cmz97/ai-eink/asciiTable_1.5x.png

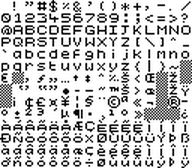
asciiTable_1.5x.png
