cmz97/ai-eink/asciiTable_2x.png

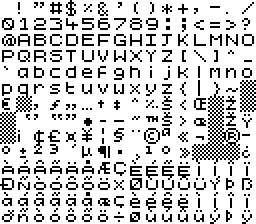
asciiTable_2x.png
