cmz97/ai-eink/asciiTable_3x.png

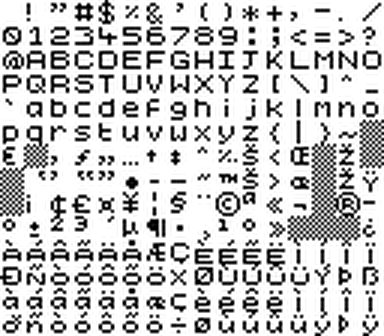
asciiTable_3x.png
