cmz97/ai-eink/Asset/Fav/3.png

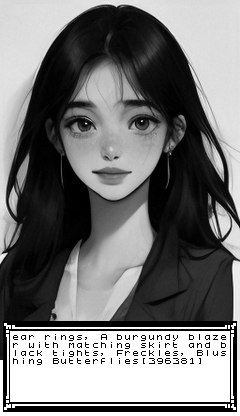
Asset/Fav/3.png
