cmz97/ai-eink/Asset/Fav/4.png

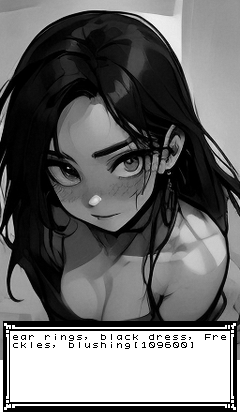
Asset/Fav/4.png
