cmz97/ai-eink/Asset/Fav/6.png

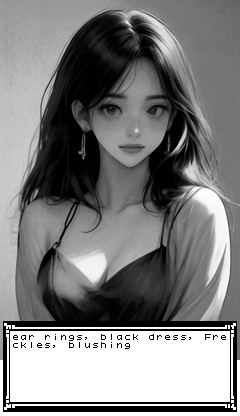
Asset/Fav/6.png
