cmz97/ai-eink/Asset/Fav/7.png

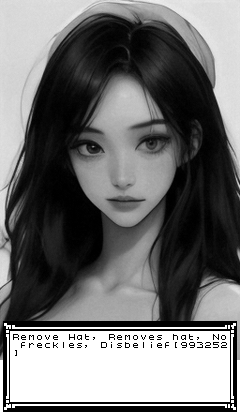
Asset/Fav/7.png
