cmz97/ai-eink/Asset/Fav/8.png

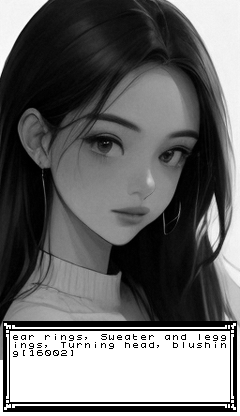
Asset/Fav/8.png
