cmz97/ai-eink/Asset/Fav/10.png

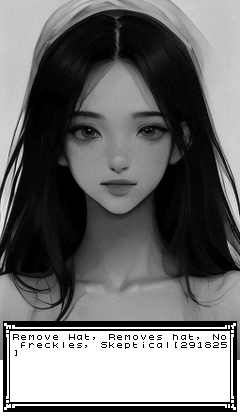
Asset/Fav/10.png
