cmz97/ai-eink/Asset/Fav/11.png

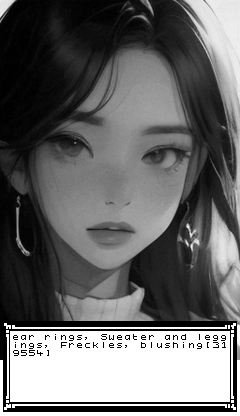
Asset/Fav/11.png
