cmz97/ai-eink/Asset/Fav/fr_00.png

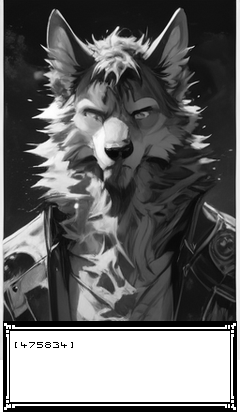
Asset/Fav/fr_00.png
