cmz97/ai-eink/Asset/Fav/men_00.png

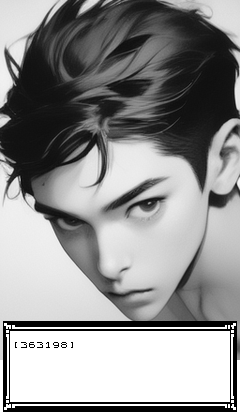
Asset/Fav/men_00.png
