cmz97/ai-eink/Asset/Fav/men_01.png

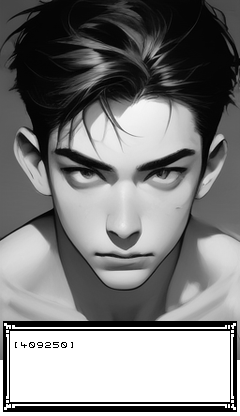
Asset/Fav/men_01.png
