cmz97/ai-eink/PCB/AI_EINK.png

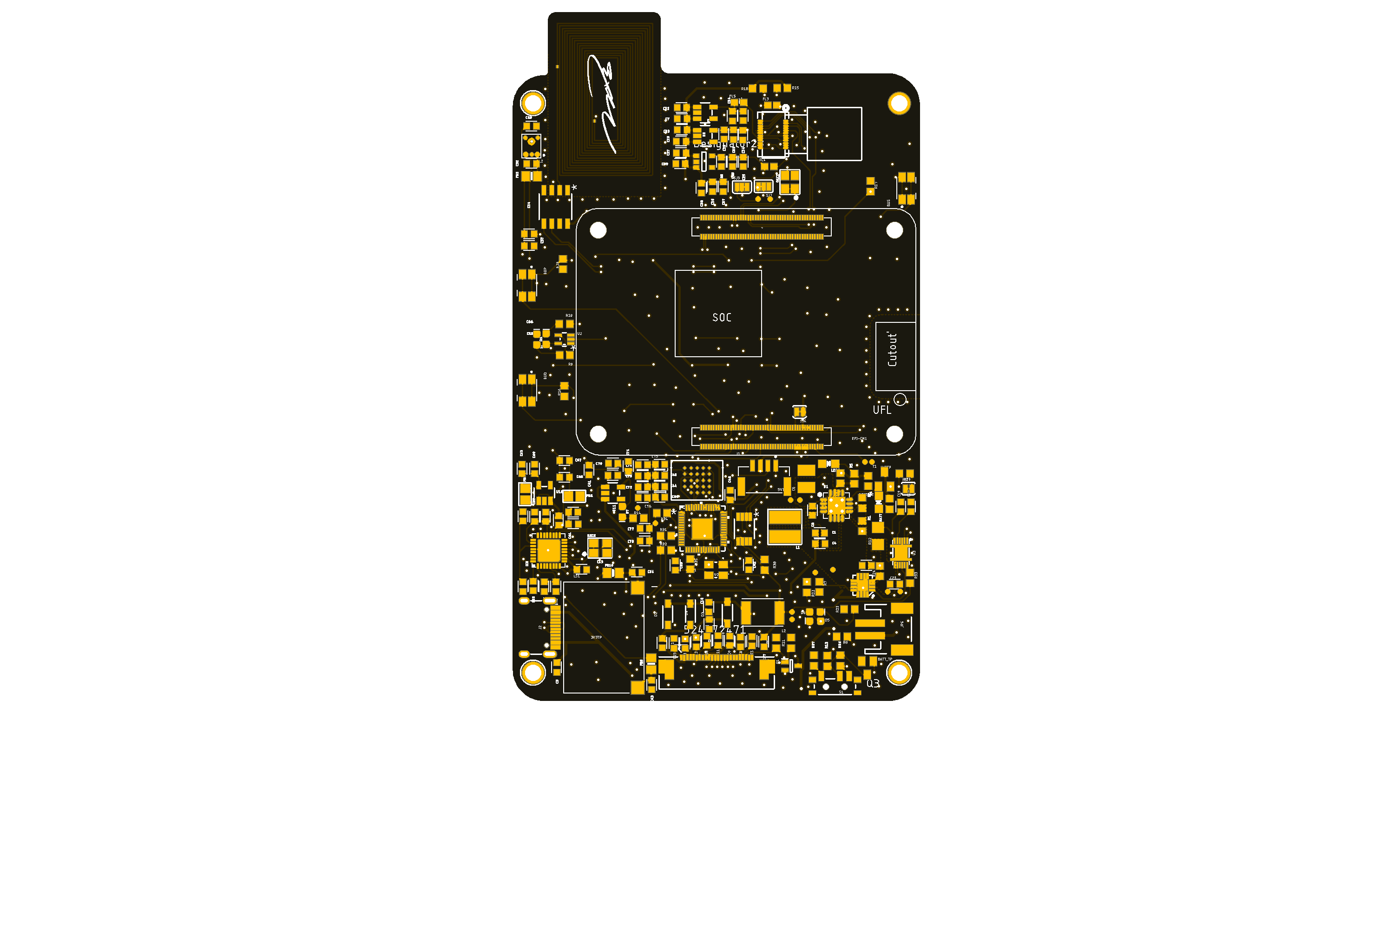
PCB/AI_EINK.png
