cmz97/ai-eink/Playground/1.png

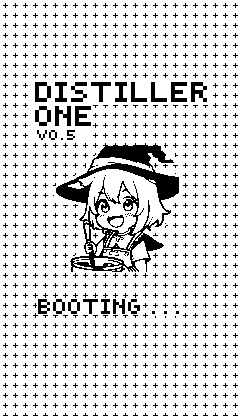
Playground/1.png
