cmz97/ai-eink/Playground/2.png

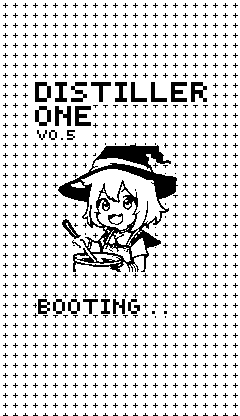
Playground/2.png
