cmz97/ai-eink/Playground/combined_image.bmp

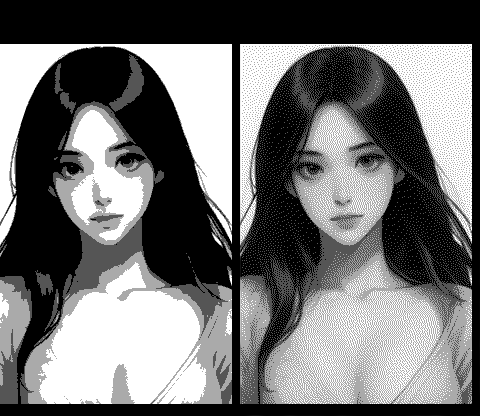
Playground/combined_image.bmp
