cmz97/ai-eink/Playground/image_normal.bmp

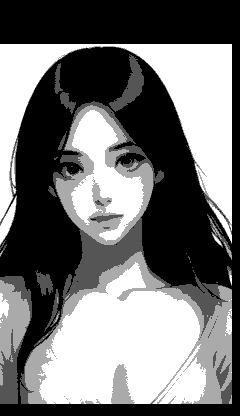
Playground/image_normal.bmp
