cmz97/ai-eink/tamagochiChar/clean/animation_0.png

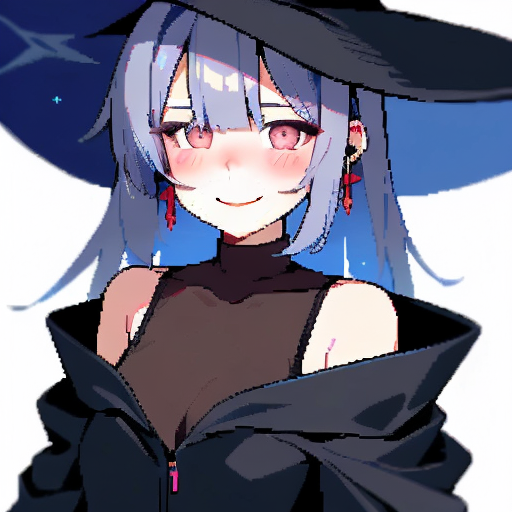
tamagochiChar/clean/animation_0.png
