cmz97/ai-eink/temp-Portraits-2.5D.png

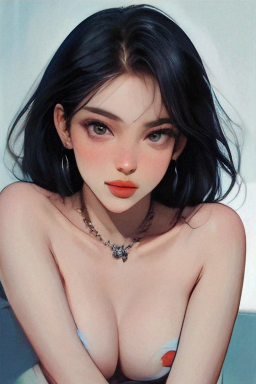
temp-Portraits-2.5D.png
