cmz97/ai-eink/Playground/result.bmp

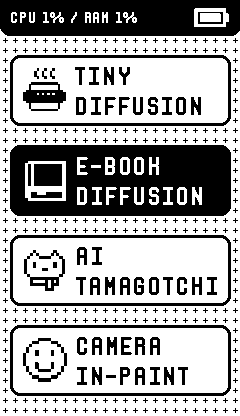
Playground/result.bmp
