cmz97/ai-eink/Playground/test_gui.png

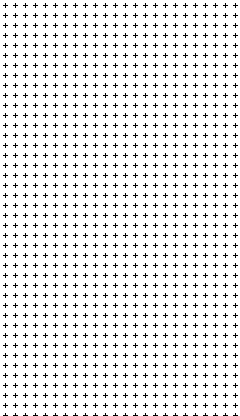
Playground/test_gui.png
