cmz97/ai-eink/app_ebook_kid.py

import subprocess
import threading
import queue
import asyncio
import os
import sys
import time 
import random
import json
from pathlib import Path
from einkDSP import einkDSP
from encoder import Encoder, Button, MultiButtonMonitor
from PIL import Image
from utils import * 
import threading  # Import threading module
import RPi.GPIO as GPIO
from apps import SdBaker, PromptsBank, BookLoader, SceneBaker
import logging
logging.basicConfig(level=logging.INFO, format='%(asctime)s - %(levelname)s - %(message)s')
# GPIO.cleanup()
from Ebook_GUI import EbookGUI

def format_text(line_buffer, word, boxWidth, boxHeight, fontWidth, fontHeight):
        # line buffer -> <line_idx, words>
        charsPerLine = boxWidth // fontWidth
        linesPerPage = boxHeight // fontHeight
        # assume buffer = list of words

        lineLength = len(" ".join(line_buffer[-1])) if line_buffer else 0
        # handle corner case
        if len(word) > charsPerLine:  # need to break word
            return line_buffer + word[:charsPerLine], False
            
        if lineLength + len(word) + (1 if line_buffer else 0) <= charsPerLine: # append and update
            if line_buffer:
                line_buffer[-1].append(word)
            else:
                line_buffer = [[word]]
        else: # new line
            # check if new page
            if len(line_buffer) >= linesPerPage: # new page
                return [[word]] , True
            line_buffer.append([word])

        # update buffer and return
        return line_buffer , False

class Controller:

    def __init__(self):
        self.eink = einkDSP()
        # self.butUp = Button(9, direction='up', callback=self.press_callback) # gpio 26
        # self.butDown = Button(22, direction='down', callback=self.press_callback) # gpio 26
        # self.butEnter = Button(17, direction='enter', callback=self.press_callback) # gpio 26

        buttons = [
            {'pin': 9, 'direction': 'up', 'callback': self.press_callback},
            {'pin': 22, 'direction': 'down', 'callback': self.press_callback},
            {'pin': 17, 'direction': 'enter', 'callback': self.press_callback}
        ]
        
        self.multi_button_monitor = MultiButtonMonitor(buttons)


        self.in_4g = True
        self.image = gui.canvas
        
        # buffers
        self.prompt_buffer = ""
        self.text_buffer = []
        self.image_buffer = []

        # threading issues
        self.locked = False
        self.cooking = False
        self.pending_image = False
        self.pending_story = False



    def background_task(self):
        self.sd_process(self.prompt_buffer)

    def transit(self):
        self.locked = True
        self.eink.epd_init_fast()
        self.eink.PIC_display_Clear()
        logging.info('transit to 2g done')
    
    def clear_screen(self):
        gui.clear_page()
        image = Image.new("L", (eink_width, eink_height), "white")
        hex_pixels = dump_1bit(np.array(image.transpose(Image.FLIP_TOP_BOTTOM), dtype=np.uint8))
        self.eink.epd_init_part()
        self.eink.PIC_display(hex_pixels)

    def part_screen(self, hex_pixels):
        self.locked = True
        self.eink.epd_init_part()
        self.eink.PIC_display(hex_pixels)
        self.locked = False
        
    def full_screen(self, hex_pixels):
        self.eink.epd_w21_init_4g()
        self.eink.pic_display_4g(hex_pixels)
        self.eink.epd_sleep()

    def _status_check(self):
        if self.in_4g : 
            self.transit()
            self.in_4g = False
        
    def _fast_text_display(self, text="loading ..."):
        image = fast_text_display(self.image, text)
        grayscale = image.transpose(Image.FLIP_TOP_BOTTOM).convert('L')
        hex_pixels = dump_1bit_with_dithering(np.array(grayscale, dtype=np.float32))
        # hex_pixels = dump_1bit(np.array(image.transpose(Image.FLIP_TOP_BOTTOM), dtype=np.uint8))
        self.part_screen(hex_pixels)

    def update_screen(self, image = None):
        if not image : image = self.image
        # image = self._prepare_menu(self.image)
        # update screen
        grayscale = image.transpose(Image.FLIP_TOP_BOTTOM).convert('L')
        logging.info('preprocess image done')
        hex_pixels = dump_1bit_with_dithering(np.array(grayscale, dtype=np.float32))
        logging.info('2bit pixels dump done')
        self.part_screen(hex_pixels)

    def load_model(self):
        logger.info("loading model")
        self._fast_text_display('loading sd model ~10sec')
        sd_baker.load_model(
            '/home/kevin/ai/models/sdxs-512-dreamshaper-onnx',
            "sdxs",
            "")
        self.show_options()

    def trigger_background_job(self):
        self.cooking = True
        logger.info("background_task triggered")
        background_thread = threading.Thread(target=self.background_task, daemon=True)
        background_thread.start()
        # update flag
        self.pending_image = False
        logger.info("pending image flag off")

    def sd_process(self, prompts):
        sd_baker._generate_image_thread(prompts, self.sd_image_callback, "temp-ebook-kid")
        
    def sd_image_callback(self, image):
        self.image_buffer.append(image)
        # image finished cooking done
        self.cooking = False

    async def show_last_image(self):
        if self.image_buffer:
            image = insert_image(self.image, self.image_buffer.pop(0))
            hex_pixels = image_to_header_file(image)
            self.clear_screen()
            self.full_screen(hex_pixels)
            self.in_4g = True
            self.locked = False
            await asyncio.sleep(10)  # Properly await sleeping


    def show_options(self):
        self.clear_screen()
        image_with_dialog = apply_dialog_box(
                input_image = self.image,
                dialog_image = ui_assets["small_dialog_box"]["image"],
                box_mat = [text_to_image("[new story]")],
                highligh_index = 0,
                placement_pos = ui_assets["small_dialog_box"]["placement_pos"]
            )
        self.update_screen(image_with_dialog)        
    
    def stream_text(self, text):
        self._status_check()
        # screen_buffer = 10
        w, h = gui.text_area[1][0] - gui.text_area[0][0] , gui.text_area[1][1] - gui.text_area[0][1]
        scale = 0.55
        self.text_buffer, new_page = format_text(
            self.text_buffer, 
            text, 
            boxWidth= w,
            boxHeight= h,
            fontWidth=gui.font_size * scale, 
            fontHeight=gui.font_size * 1.4 * scale)

        # call for screen update
        if new_page : gui.clear_page()
        self.image = gui.draw_text_on_canvas(gui.canvas, [" ".join(x) for x in self.text_buffer])
        self.update_screen()        

    def press_callback(self, key): 
        # only key needed to gen a new story
        if key == "enter" and not self.pending_story:
            self.pending_story = True
            self._fast_text_display("preparing the story...")

    def sd_check(self):
        if self.prompt_buffer.endswith('.') : # send to prompt
            if not self.cooking : self.trigger_background_job()
            self.prompt_buffer = "" # refresh
        else:
            pass 

def run_c_executable(model_file, temperature, max_token, prompt, output_queue):
    command = f"/home/kevin/ai/llama2.c/run {model_file} -t {temperature} -n {max_token} -i \"{prompt}\""
    with subprocess.Popen(command, shell=True, stdout=subprocess.PIPE, universal_newlines=True, bufsize=1) as proc:
        for output in proc.stdout:
            if output.strip() == '':  # Check for an empty string indicating no more output
                break
            words = output.split()
            for word in words:
                output_queue.put(word)

        proc.stdout.close()
        return_code = proc.wait()
        if return_code:
            raise subprocess.CalledProcessError(return_code, command)

    output_queue.put(None)  # Ensure to put None after the subprocess ends

async def async_output_generator(output_queue):
    while True:
        output = await asyncio.to_thread(output_queue.get)  # Blocking get offloaded to a thread
        if output is None:
            break
        yield output

def run_c_executable_async(model_file, temperature, max_token, prompt, output_queue):
    thread = threading.Thread(target=run_c_executable, args=(model_file, temperature, max_token, prompt, output_queue))
    thread.start()
    return thread

async def start_story():
    output_queue = queue.Queue()
    c_thread = run_c_executable_async(model_file, temperature, max_token, prompt, output_queue)
    try:
        async for output in async_output_generator(output_queue):
            # print(output)  # Or handle the output as needed
            # pass in word to buffer
            await controller.show_last_image()        
            controller.stream_text(output)
            controller.prompt_buffer += " " + output
            controller.sd_check()
    finally:
        c_thread.join()
        output_queue.put(None)  # Signal the generator that the process is done
    logging.info("done with async_output_generator")
    # last image check
    while controller.cooking:
        await controller.show_last_image()        

# Example usage
model_file = "/home/kevin/ai/llama2.c/stories110M.bin"
temperature = 0.7
max_token = 50
prompt = "Once upon a time in the animal kindom world,  "    

# hardcoded parts
gui = EbookGUI()
controller = Controller()
sd_baker = SdBaker(vae_override="../models/sdxs-512-0.9/vae")
# override sd 
sd_baker.neg_prompt = "bad hand, bad face, worst quality, low quality, logo, text, watermark, username, harsh shadow, shadow, artifacts, blurry, smooth texture, bad quality, distortions, unrealistic, distorted image, bad proportions, duplicate"
sd_baker.char_id = "masterpiece, lineart, cute drawing, chibi, detailed story illustration, fantacy story,"
sd_baker.num_inference_steps = 1
controller.load_model()

# Example usage
if __name__ == "__main__":
    try:
        while True:
            time.sleep(1)
            if controller.pending_story:
                # Manually setting up the event loop
                loop = asyncio.new_event_loop()
                asyncio.set_event_loop(loop)
                try:
                    loop.run_until_complete(start_story())
                finally:
                    loop.close() 
                logging.info("out of start_story loop")
                controller.pending_story = False
                controller.show_options() # for next
                # just show option page
            # backCounter += 1 if GPIO.input(9) == 1 else 0
            # if backCounter >= 5:
            #     os._exit(0)
    except Exception:
        # logger.errors(e)
        pass
