cmz97/ai-eink/app_tiny_diffusion.py

# from sshkeyboard import listen_keyboard
import os
import sys
import time 
import random
import json
from pathlib import Path
from einkDSP import einkDSP
from encoder import *
from PIL import Image
from utils import * 
import threading  # Import threading module
import RPi.GPIO as GPIO
from apps import SdBaker, PromptsBank
import logging
logging.basicConfig(level=logging.INFO, format='%(asctime)s - %(levelname)s - %(message)s')
GPIO.cleanup()

class Controller:

    def __init__(self):
        self.eink = einkDSP()
        
        buttons = [
            {'pin': 9, 'direction': 'up', 'callback': self.press_callback},
            {'pin': 22, 'direction': 'down', 'callback': self.press_callback},
            {'pin': 17, 'direction': 'enter', 'callback': self.press_callback}
        ]
        self.multi_button_monitor = MultiButtonMonitor(buttons)

        self.in_4g = True
        self.image = Image.new("L", (eink_width, eink_height), "white")
        self.model = None
        
        # UI states
        self.page = 0 # 0 : main ,  1: display,  2 : play
        self.pending_swap_prompt = None
        self.current_screen_selects = []
        self.layout = {
            0 : self._model_select_page,
            1 : self._display_page,
            2 : self._edit_prompt_page_0,
            3 : self._edit_prompt_page_1,
            4 : self._image_browser,
        }
        self.selection_idx = [0] * len(self.layout)
        self.display_cache = {
            1 : [text_to_image("[edit prompts]"), text_to_image("[generate]"), text_to_image("[back]")],
            2 : [text_to_image(f"{group}") for group in pb.prompt_groups] + [text_to_image("[back]")],
            3 : [] # pending to be init
        }
        
        logging.info('Controller instance created')

        # threading issues
        self.locked = False
        self.loading_screen_thread = None
        self.stop_loading_event = threading.Event()

        # model specific
        self.trigger_words = []

        # browsing temps
        self.browsing_file_list = [] 

    def _reload_prompt_cache(self):
        self.display_cache[3] = [
            [text_to_image(prompt)
            for prompt in prompts]
            for prompts in pb.prompt_selections
        ]

    def _update_prompt_cache(self, idx):
        self.display_cache[3][idx] = [text_to_image(prompts) for prompts in pb.prompt_selections[idx]]
        
    def start_loading_screen(self):
        self.locked = True
        logging.info("start_loading_screen thread ")
        self.stop_loading_event.clear()
        if self.loading_screen_thread is None or not self.loading_screen_thread.is_alive():
            self.loading_screen_thread = threading.Thread(target=self.show_loading_screen)
            self.loading_screen_thread.start()

    def stop_loading_screen(self):
        logging.info("stop_loading_screen thread ")
        self.stop_loading_event.set()
        if self.loading_screen_thread:
            self.loading_screen_thread.join()
            self.loading_screen_thread = None
        self.clear_screen()

    def show_loading_screen(self):
        self.locked = True
        start_time = time.time()
        frame0 = paste_loadingBox(self.image, frame=0)
        frame1 = paste_loadingBox(self.image, frame=1)
        frame0 = draw_text_on_dialog("COOKING...", frame0, (eink_width//2, eink_height//3*2), (eink_width//2+50, eink_height//3*2), True)
        frame1 = draw_text_on_dialog("COOKING...", frame1, (eink_width//2, eink_height//3*2), (eink_width//2+50, eink_height//3*2), True)
            
        while not self.stop_loading_event.is_set():
            draw_text_on_img("{:.0f}s".format(time.time() - start_time), frame0)            
            pixels = dump_1bit_with_dithering(np.array(frame0.transpose(Image.FLIP_TOP_BOTTOM), dtype=np.float32)) 
            self.part_screen(pixels)
            time.sleep(0.5)
            draw_text_on_img("{:.0f}s".format(time.time() - start_time), frame1)
            pixels = dump_1bit_with_dithering(np.array(frame1.transpose(Image.FLIP_TOP_BOTTOM), dtype=np.float32)) 
            self.part_screen(pixels)
            time.sleep(0.5)

        self.locked = False

    def transit(self):
        # self.locked = True
        self.eink.epd_init_fast()
        self.eink.PIC_display_Clear()
        logging.info('transit to 2g done')
    
    def clear_screen(self):
        image = Image.new("L", (eink_width, eink_height), "white")
        hex_pixels = dump_1bit(np.array(image.transpose(Image.FLIP_TOP_BOTTOM), dtype=np.uint8))
        self.eink.epd_init_part()
        self.eink.PIC_display(hex_pixels)

    def part_screen(self, hex_pixels):
        self.locked = True
        self._status_check() # 4g to 2g check
        self.eink.epd_init_part()
        self.eink.PIC_display(hex_pixels)
        self.locked = False
        
    def full_screen(self, hex_pixels):
        self.eink.epd_w21_init_4g()
        self.eink.pic_display_4g(hex_pixels)
        self.eink.epd_sleep()

    def _status_check(self):
        if self.in_4g : 
            self.transit()
            self.in_4g = False
    
    def refresh_2g(self, image):
        # update screen
        grayscale = image.transpose(Image.FLIP_TOP_BOTTOM).convert('L')
        hex_pixels = dump_1bit_with_dithering(np.array(grayscale, dtype=np.float32))
        self.part_screen(hex_pixels) 

    def update_screen(self):
        image = self._prepare_menu(self.image)
        # update screen
        grayscale = image.transpose(Image.FLIP_TOP_BOTTOM).convert('L')
        logging.info('preprocess image done')
        hex_pixels = dump_1bit_with_dithering(np.array(grayscale, dtype=np.float32))
        logging.info('2bit pixels dump done')
        self.part_screen(hex_pixels)

    def load_model(self, model_path, model_info):
        self.locked = True
        self.transit()

        # just show one static image with loading , I'm sure load_model() blocks all threads
        image = Image.new("L", (eink_width, eink_height), "white")
        image = paste_loadingBox(image, frame=0)
        image = draw_text_on_dialog("LOADING MODEL ...", image, (eink_width//2-150, eink_height//2), (eink_width//2+150, eink_height//2), True)
        pixels = dump_1bit_with_dithering(np.array(image.transpose(Image.FLIP_TOP_BOTTOM), dtype=np.float32))
        self.part_screen(pixels)
        sd_baker.load_model(model_path, model_info['name'], model_info['trigger_words'])

        # check for some overrides
        if "neg_prompt" in model_info: sd_baker.neg_prompt = model_info['neg_prompt']
        if "vae" in model_info: sd_baker.load_vae(model_info['vae'])
        if "num_inference_steps" in model_info: sd_baker.num_inference_steps = model_info['num_inference_steps']

        self.locked = False
        
    def _model_select_page(self, key): # main page
        self.locked = True
        # sync status
        self.page = 0
        
        # process key
        if key == "up" : self.selection_idx[self.page] += 1 
        elif key == "down" : self.selection_idx[self.page] -= 1 
        elif key == "enter" :  # load model
            curr_file = str(model_list[self.selection_idx[self.page]])
            with open(curr_file) as f: model_info = json.load(f)
            if model_info['name'] == "Gallery" :
                # image browsing mode 
                self._image_browser("init")
                return
            logging.info(f"enter {self.selection_idx[self.page]} , loading {curr_file}")
            self.load_model(curr_file.replace("_add_ons.json",""), model_info)
            # self.clear_screen() # clear before go to 4g
            self._display_page("init") # proceed next
            return

        # rolling        
        self.selection_idx[self.page] = self.selection_idx[self.page] % len(model_list)

        # loading resources
        curr_file = str(model_list[self.selection_idx[self.page]])
        with open(curr_file) as f: model_info = json.load(f)
        
        # thumbnail 
        thumbnail_image = render_thumbnail_page(Image.open(curr_file.replace("_add_ons.json", "thumbnail.png")), model_info['name'])
        
        # print screen
        # hex_pixels = image_to_header_file(thumbnail_image)
        
        self.refresh_2g(thumbnail_image)
        self.model = model_info['name']
        self.locked = False

    def _display_page(self, key):
        if not self.model or self.locked: return

        # status sync
        self.page = 1

        # check key states
        if key == "init" : # show last
            self.clear_screen()
            # render
            logging.info(f"enter page {self.page}")
            file_cache = f"./temp-{self.model}.png"
            if os.path.exists(file_cache): # reload
                image = Image.open(file_cache)
                prompt_str = image.info.get("prompt")
                pb.load_prompt(prompt_str)  
                self._reload_prompt_cache()
                self.sd_image_callback(image)
            else: # show empty, init dependencies
                # pb.fresh_prompt_selects()
                self._reload_prompt_cache()
                image = Image.new("L", (eink_width, eink_height), "white")
                self.image_callback(image)
            return 
        
        if key == "up" : self.selection_idx[self.page] -= 1
        elif key == "down" : self.selection_idx[self.page] += 1
        elif key == "enter" :  # hit prompt selection
            if self.selection_idx[self.page] == 0: 
                self._edit_prompt_page_0("init")
                return
            elif self.selection_idx[self.page] == 1:
                self._butSubmit()
                return 
            else:
                self._model_select_page("")
                return

        # rolling pin
        self.selection_idx[self.page] = self.selection_idx[self.page] % len(self.display_cache[self.page])
        # update screen
        self.update_screen()        

    def _edit_prompt_page_0(self, key): # display page + prompt select
        if not self.model or self.locked: return

        # status sync
        self.page = 2    
            
        if key == "up" : self.selection_idx[self.page] -= 1 
        elif key == "down" : self.selection_idx[self.page] += 1 
        elif key == "enter" :  # hit prompt selection
            if self.selection_idx[self.page] != len(self.display_cache[self.page])-1:
                # update and fresh new screen selects
                self._edit_prompt_page_1("init")
                return
            else:
                self._display_page("")
                return

        # rolling pin
        self.selection_idx[self.page] = self.selection_idx[self.page] % len(self.display_cache[self.page])
        # update screen
        self.update_screen()        

    def _edit_prompt_page_1(self, key): # prompt tuning
        # status sync
        self.page = 3
        if key == "init":
            self.update_screen()
            return
        if key == "up" : self.selection_idx[self.page] -= 1 
        elif key == "down" : self.selection_idx[self.page] += 1 
        elif key == "enter" :
            if self.selection_idx[self.page] == 0: 
                self._edit_prompt_page_0("")
                return # no change    
            # swap the prompt
            pb.update_prompt(self.selection_idx[self.page-1], self.selection_idx[self.page])
            # refresh cache
            self._update_prompt_cache(self.selection_idx[self.page-1])
            self.selection_idx[self.page] = 0 
            # back to last page
            self._edit_prompt_page_0("")
            return
        
        # rolling pin
        self.selection_idx[self.page] = self.selection_idx[self.page] % pb.selection_num # include self
        
        # update screen
        self.update_screen()

    def _butSubmit(self):
        # reset some status
        # self.selection_idx[self.page] = 0
        # run sd and render
        self.start_loading_screen()
        self.sd_process()
        pb.fresh_prompt_selects()
        self._reload_prompt_cache()


    def _image_browser(self, key):
        self.page = 4
        def load_cache():
            images_dir = './Asset/Fav'
            image_files = [f for f in os.listdir(images_dir) if f.endswith('.png')]
            self.browsing_file_list = [f"{images_dir}/{f}" for f in image_files]
            self.browsing_file_list.sort() 
            return [text_to_image(f) for f in self.browsing_file_list] + [text_to_image("[back]")]

        if key == "init":
            # init dialog cache
            self.display_cache[self.page] = load_cache()
            # display first image
            image = Image.open(self.browsing_file_list[0])
            self.image_callback(image)
            return

        if key == "up" : self.selection_idx[self.page] -= 1 
        elif key == "down" : self.selection_idx[self.page] += 1 
        elif key == "enter" :  # load image
            if self.selection_idx[self.page] == len(self.display_cache[self.page])-1:
                # back to main page
                self._model_select_page("init")
                return
            image = Image.open(self.browsing_file_list[self.selection_idx[self.page]])
            self.image_callback(image)
            return

        # rolling        
        self.selection_idx[self.page] = self.selection_idx[self.page] % len(self.display_cache[self.page])

        # update screen
        self.update_screen()    

    def sd_process(self, prompts=None):
        if not prompts: prompts = pb.to_str() 
        # Start a new thread for the loading screen
        # prepare prompt and trigger gen
        # sd_baker.generate_image(add_prompt=prompts, callback=self.sd_image_callback)
        # event.wait()
        sd_baker._generate_image_thread(prompts, self.sd_image_callback)

    def press_callback(self, key):
        if self.locked : return
        print(f"Key {key} pressed.")
        if key == "q":
            print("Quitting...")
            exit()
        
        self.layout[self.page](key)
        
    def _update_text_box(self, text):
        # case needed : submit prompt tuning and when first time into play page or enter prompt tune page
        sub_page_id = self.selection_idx[self.page-1] # get the cache based on previous page selection
        self.display_cache[self.page][sub_page_id] = get_all_text_imgs(text)

    def _prepare_menu(self, image):     
        if self.page == 1 or self.page == 2:
            # def apply_dialog_box(input_image, dialog_image, box_mat, highligh_index, placement_pos):
            image_with_dialog = apply_dialog_box(
                input_image = image,
                dialog_image = ui_assets["small_dialog_box"]["image"],
                box_mat = self.display_cache[self.page],
                highligh_index = self.selection_idx[self.page],
                placement_pos = ui_assets["small_dialog_box"]["placement_pos"]
            )
        elif self.page == 3:
            sub_page_id = self.selection_idx[self.page-1] # get the cache based on previous page selection
            image_with_dialog = apply_dialog_box(
                input_image = image,
                dialog_image = ui_assets["large_dialog_box"]["image"],
                box_mat = self.display_cache[self.page][sub_page_id],
                highligh_index = self.selection_idx[self.page],
                placement_pos = ui_assets["large_dialog_box"]["placement_pos"]
            )
        elif self.page == 4:
            image_with_dialog = apply_dialog_box(
                input_image = image,
                dialog_image = ui_assets["large_dialog_box"]["image"],
                box_mat = self.display_cache[self.page],
                highligh_index = self.selection_idx[self.page],
                placement_pos = ui_assets["large_dialog_box"]["placement_pos"]
            )

        return image_with_dialog

    def sd_image_callback(self, image):
        self.stop_loading_screen() # pause loading first
        post_img = process_image(image)
        image_with_dialog = self._prepare_menu(post_img)
        hex_pixels = image_to_header_file(image_with_dialog)
        # show and update states
        # TODO FIX THIS 2g shadow issue 
        # time.sleep(0.5)
        self.full_screen(hex_pixels)
        self.in_4g = True
        self.image = post_img
        self.locked = False
    
    def image_callback(self, image):
        self.stop_loading_screen() # pause loading first
        image_with_dialog = self._prepare_menu(image)
        hex_pixels = image_to_header_file(image_with_dialog)
        # show and update states
        # self.clear_screen()
        self.full_screen(hex_pixels)
        self.in_4g = True
        self.image = image
        self.locked = False
        

def release_callback(key):
    print(f"Key {key} released.")

# model folder
root_folder = "/home/kevin/ai/models"
model_list = [file_path for file_path in Path(root_folder).rglob("*/_add_ons.json")]

# init 
pb = PromptsBank()
sd_baker = SdBaker()
controller = Controller()
file_cache = "./temp.png"

if __name__ == "__main__":
    # sd_baker = SdBaker(pb)
    # start with main screen
    controller.layout[0]('init')
    backCounter = 0
    try:
        while True:
            time.sleep(1)
            # backCounter += 1 if GPIO.input(9) == 1 else 0
            # if backCounter >= 5:
            #     os._exit(0)
    except Exception:
        # logger.errors(e)
        pass

    GPIO.cleanup()
